Kuze2571/Wi-Fli-Zero/img/IMG_5064.jpeg

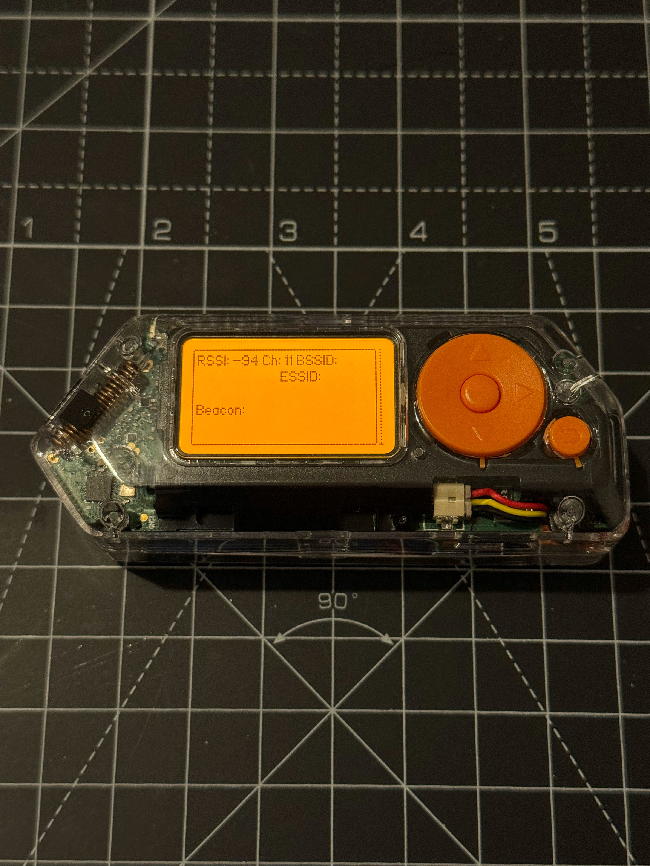
img/IMG_5064.jpeg
